kholia/HF-PA-v8/models/901-144.stp

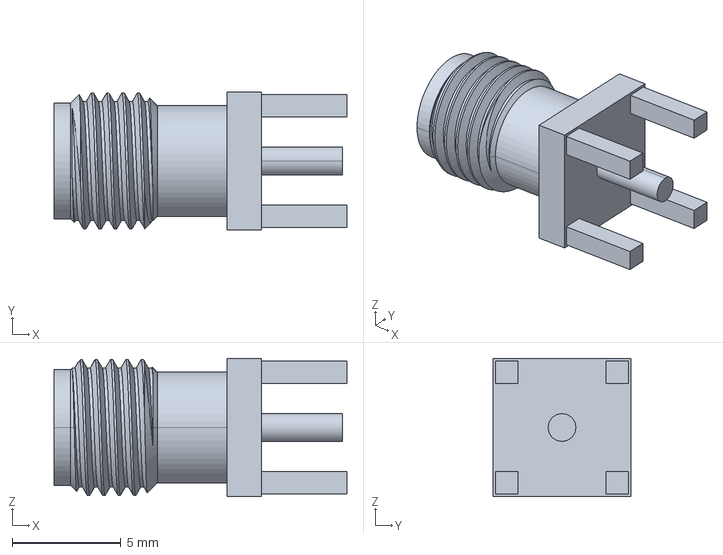
[picture p19: CAD file, 2022-11-20]
models/901-144.stp
13.5 x 6.35 x 6.35 mm
