kholia/HF-PA-v8/models/User Library-TO-92-2_54-line.STEP

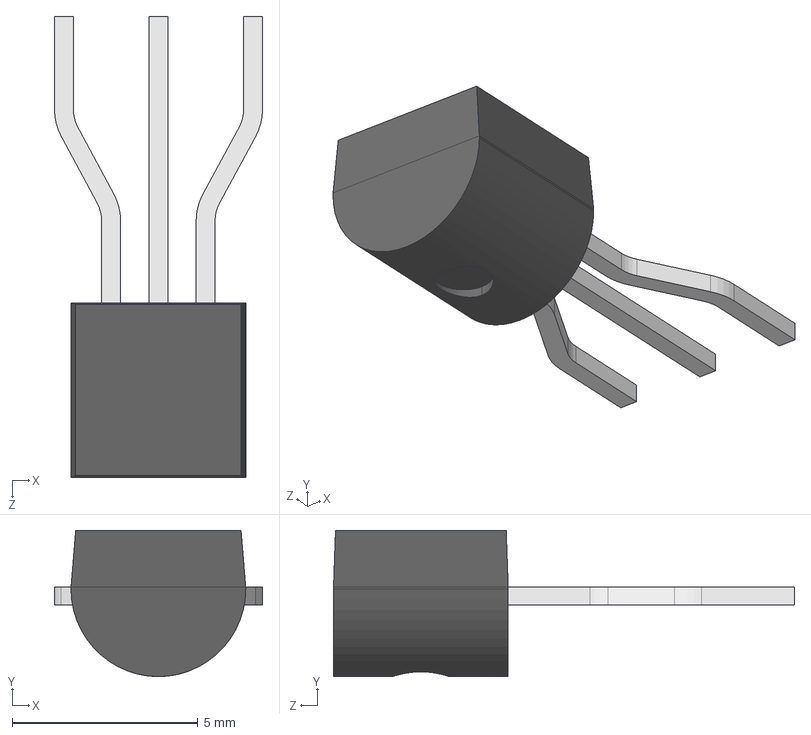
[picture p20: CAD file, 2022-11-20]
models/User Library-TO-92-2_54-line.STEP
5.60 x 3.93 x 12.4 mm
User Library-TO-92 Version2_TO-92 Part1
User Library-TO-92 Version2_TO-92 Part3
User Library-TO-92 Version2_TO-92 Part4
User Library-TO-92 Version2_TO-92 Part5
