kholia/HF-PA-v8/models/DC inductor.stl

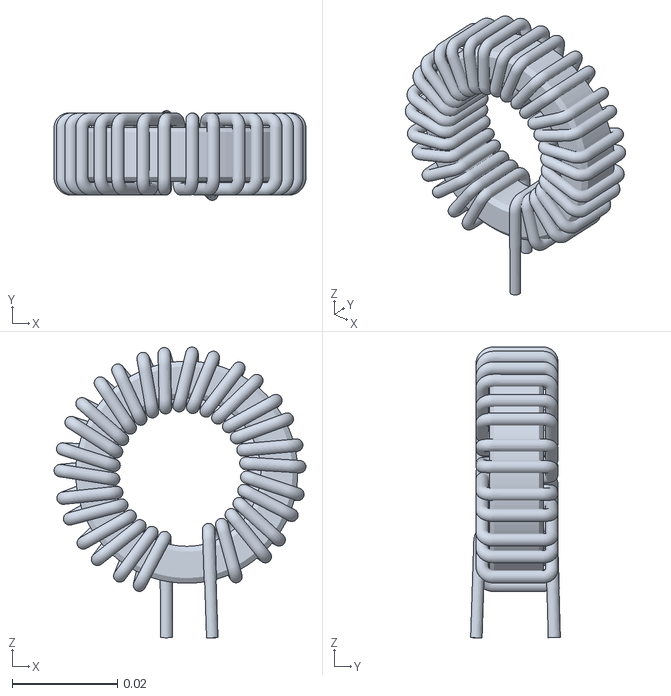
[picture p21: CAD file, 2022-11-20]
models/DC inductor.stl
0.048 x 0.0171 x 0.0554
