kholia/HF-PA-v8/models/DC-005-5A-2.0.step

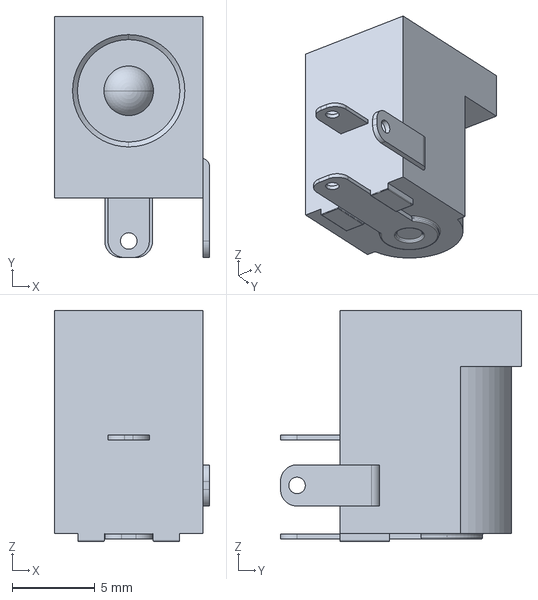
[picture p22: CAD file, 2022-11-20]
models/DC-005-5A-2.0.step
9.40 x 14.6 x 14.0 mm
